kmatthews123/Controller/board_shematic/controller board V2/controller board v2/controller board v2.jpg

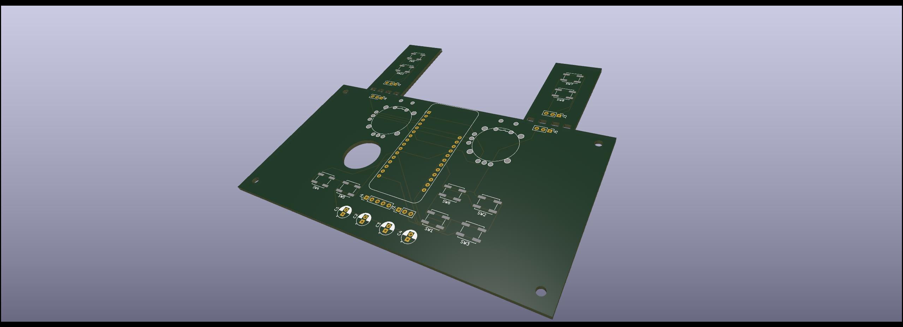
board_shematic/controller board V2/controller board v2/controller board v2.jpg
