kmatthews123/Controller/images/Controller/51d31018ed18142a5b782d5dddd84811.png

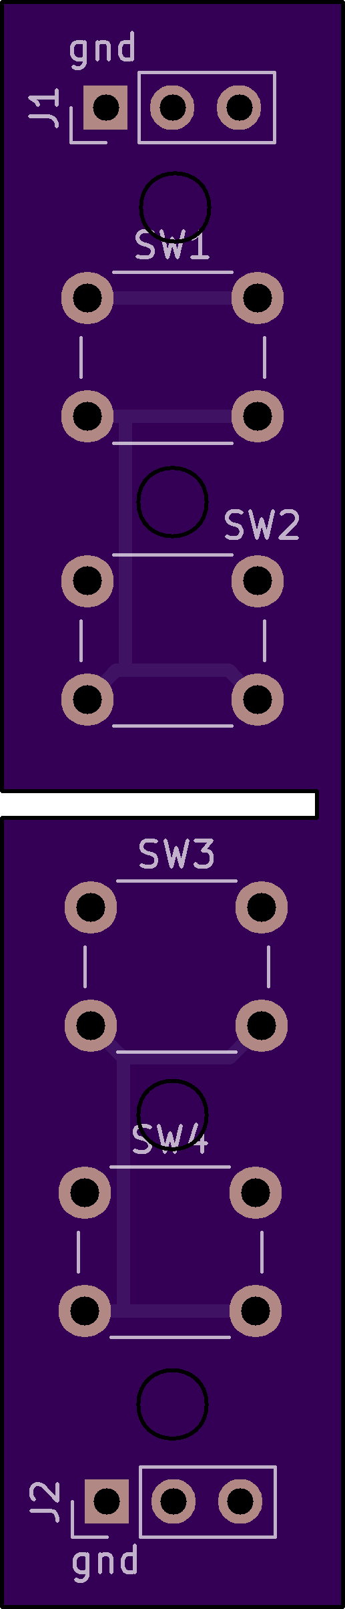
images/Controller/51d31018ed18142a5b782d5dddd84811.png
