kmatthews123/Controller/images/Controller/20240217_172748.jpg

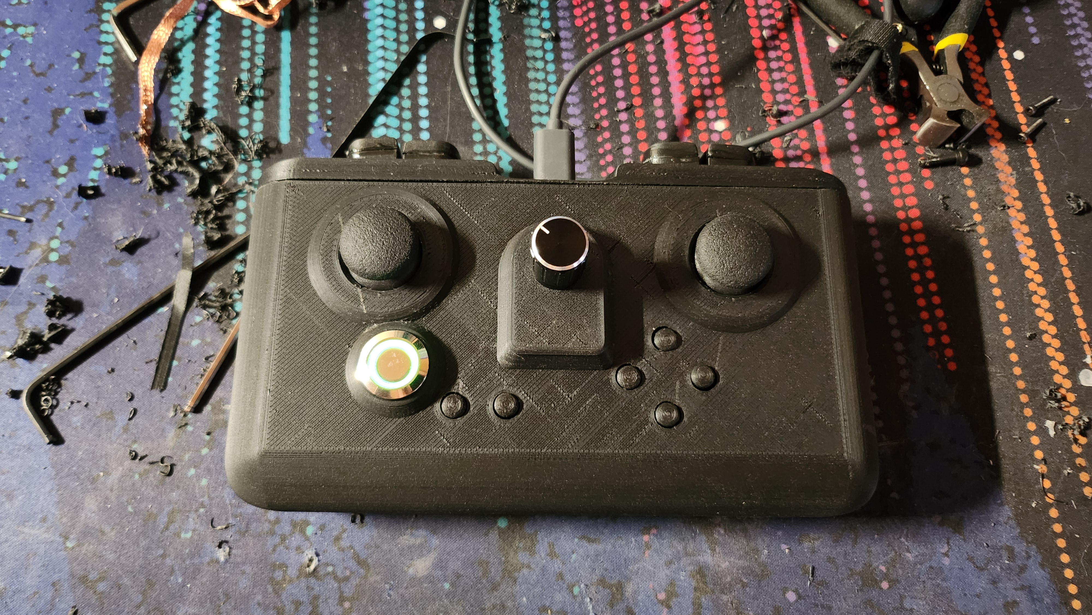
images/Controller/20240217_172748.jpg
