kmatthews123/Controller/images/Controller/20240217_172800.jpg

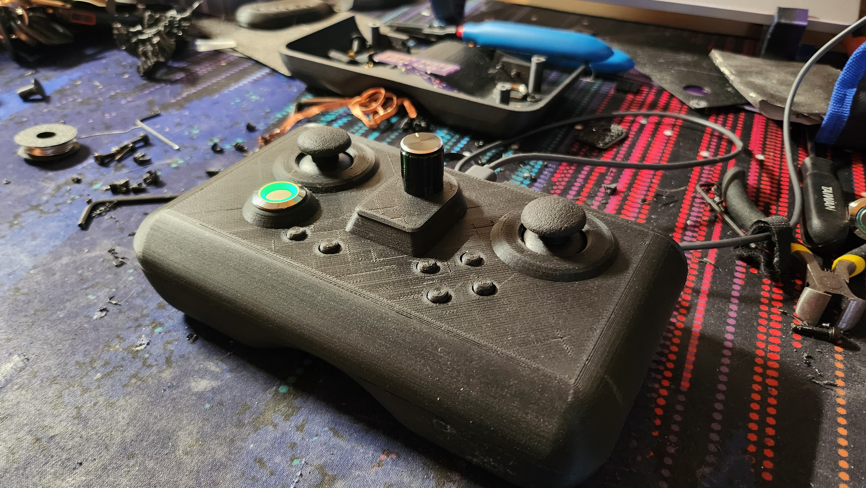
images/Controller/20240217_172800.jpg
