kmatthews123/Controller/images/Controller/20240217_172803.jpg

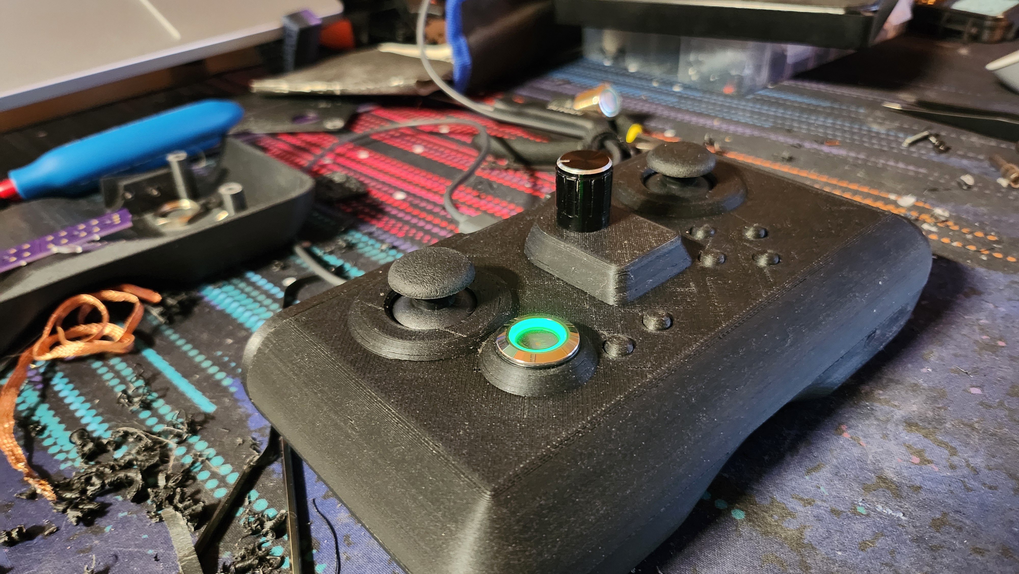
images/Controller/20240217_172803.jpg
