kmatthews123/Controller/images/Controller/20240221_180557.jpg

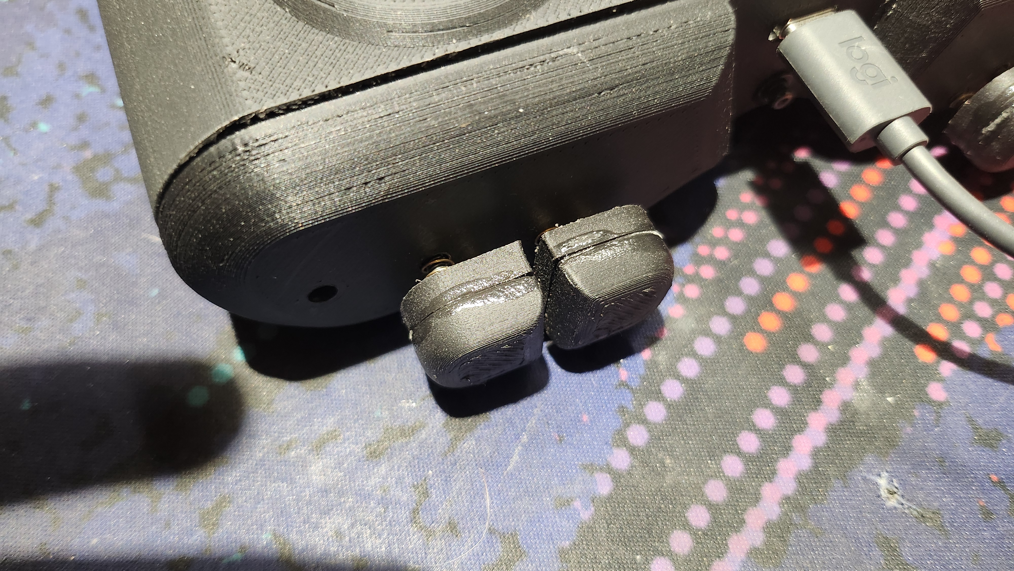
images/Controller/20240221_180557.jpg
