kmatthews123/Controller/images/Controller/20240221_180610.jpg

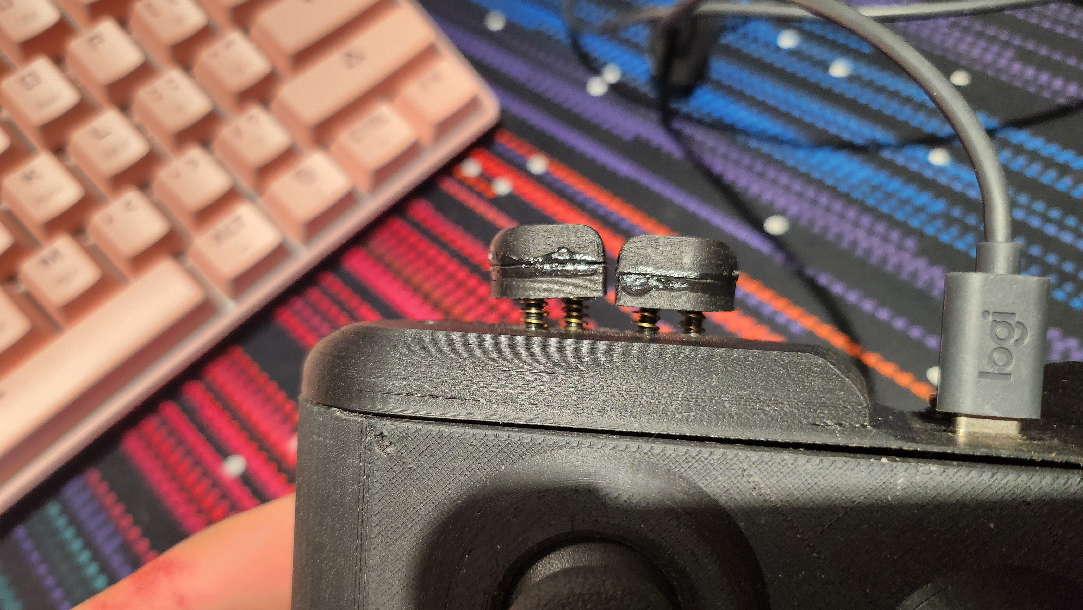
images/Controller/20240221_180610.jpg
