kmatthews123/Controller/images/Controller/20240221_180614.jpg

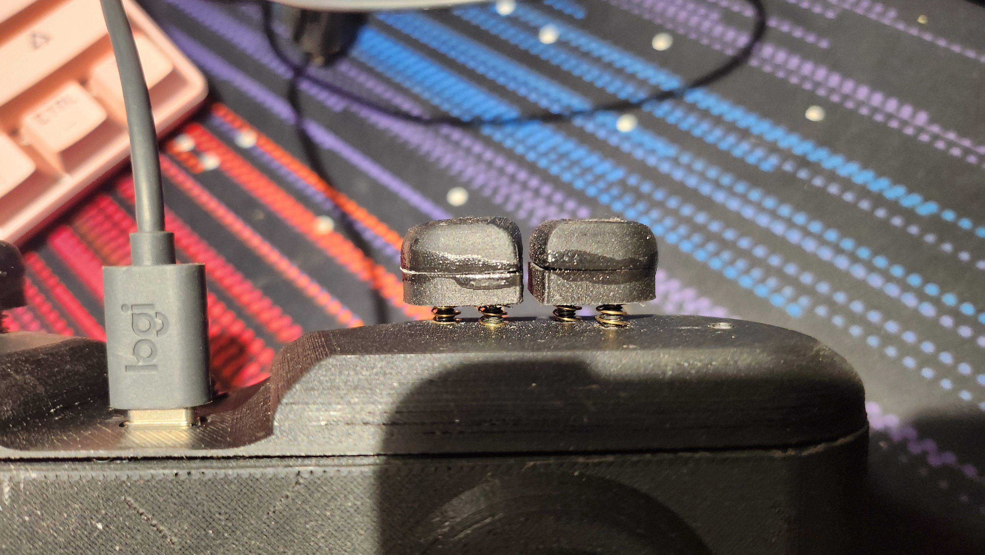
images/Controller/20240221_180614.jpg
