kmatthews123/Controller/images/Controller/controller board v2 back.png

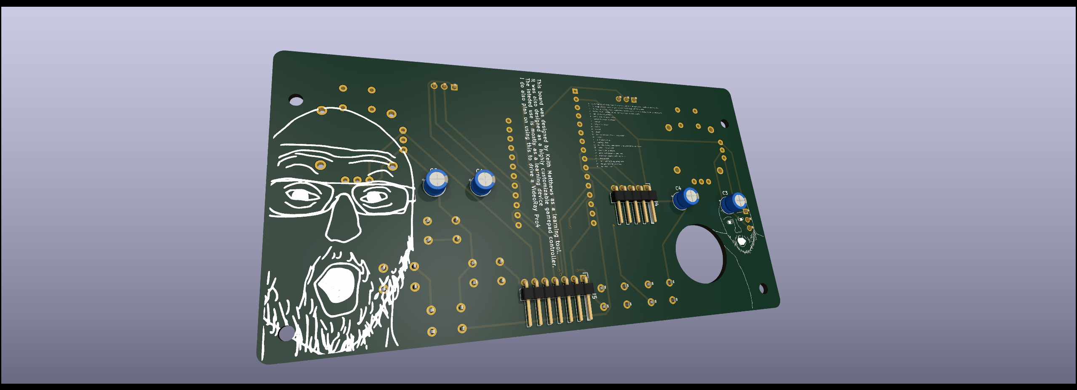
images/Controller/controller board v2 back.png
