kmatthews123/Controller/images/Controller/controller board v2.png

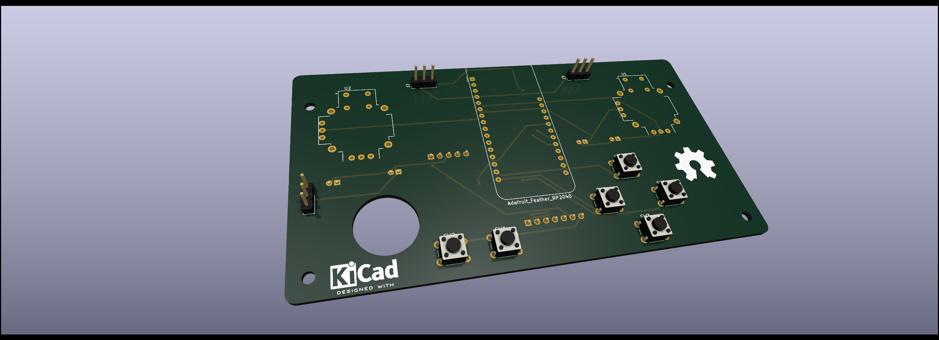
images/Controller/controller board v2.png
