kmatthews123/Controller/images/Controller/febf4503518cea3cbbaec0d58e9b9419.png

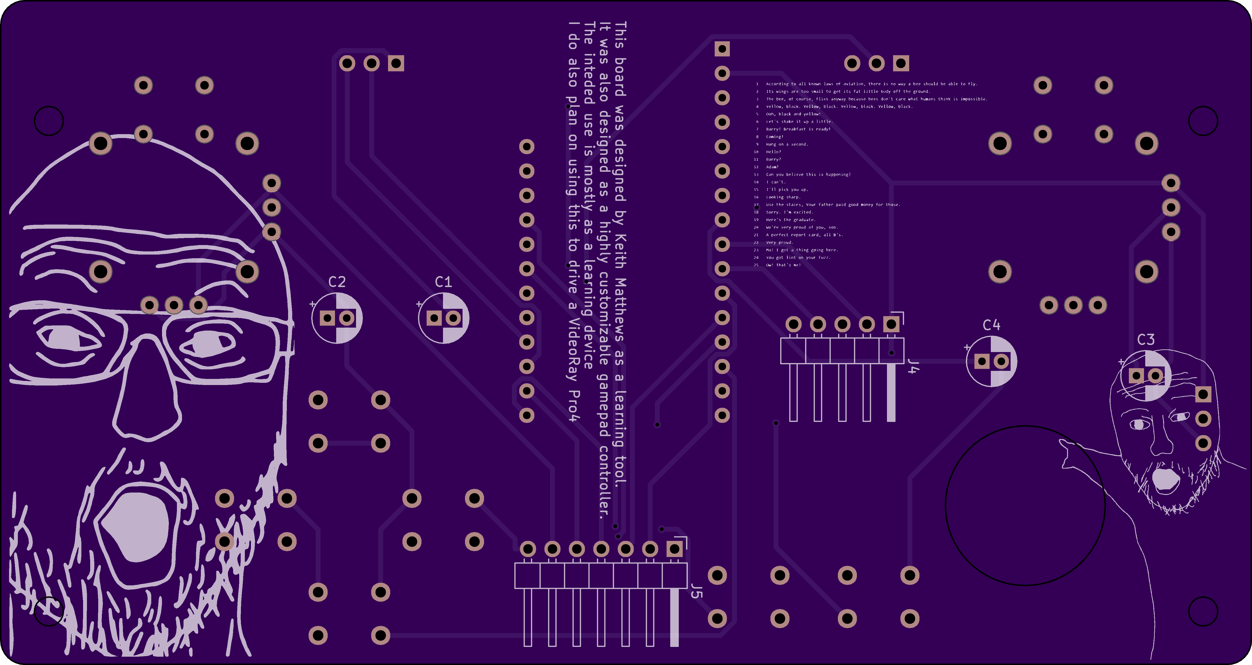
images/Controller/febf4503518cea3cbbaec0d58e9b9419.png
