kmatthews123/Controller/images/Guitar/20231124_203415.jpg

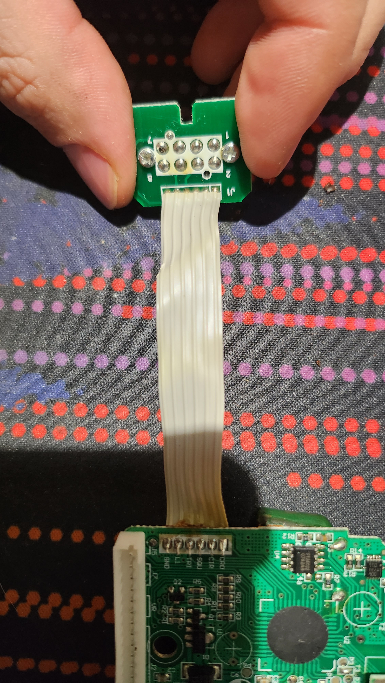
images/Guitar/20231124_203415.jpg
