kmatthews123/Controller/images/Guitar/20231124_203419.jpg

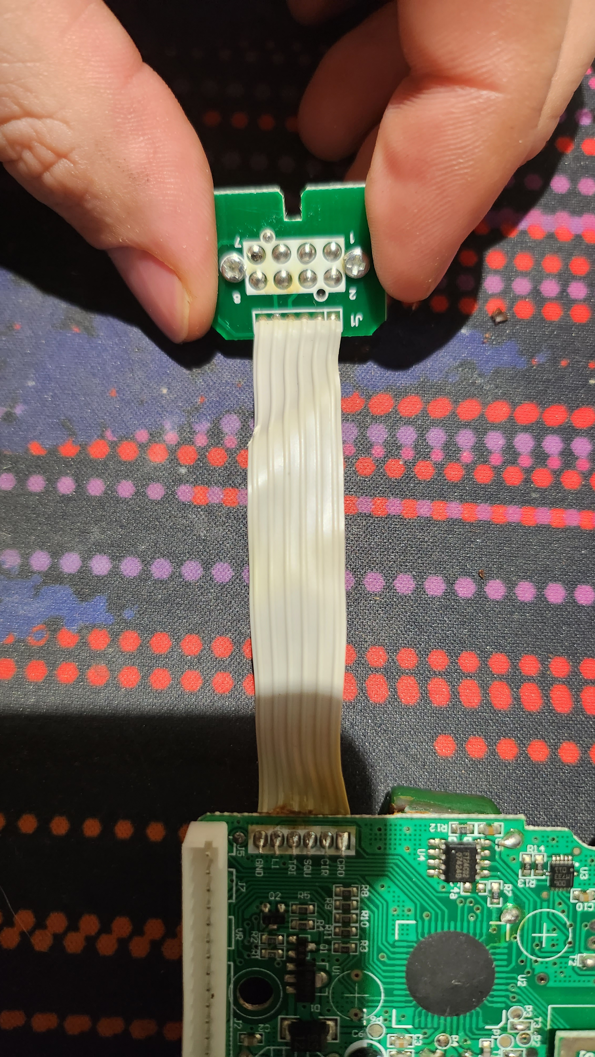
images/Guitar/20231124_203419.jpg
