kmatthews123/Controller/images/Refrence images/adafruit_products_feather-rp2040-pins.png

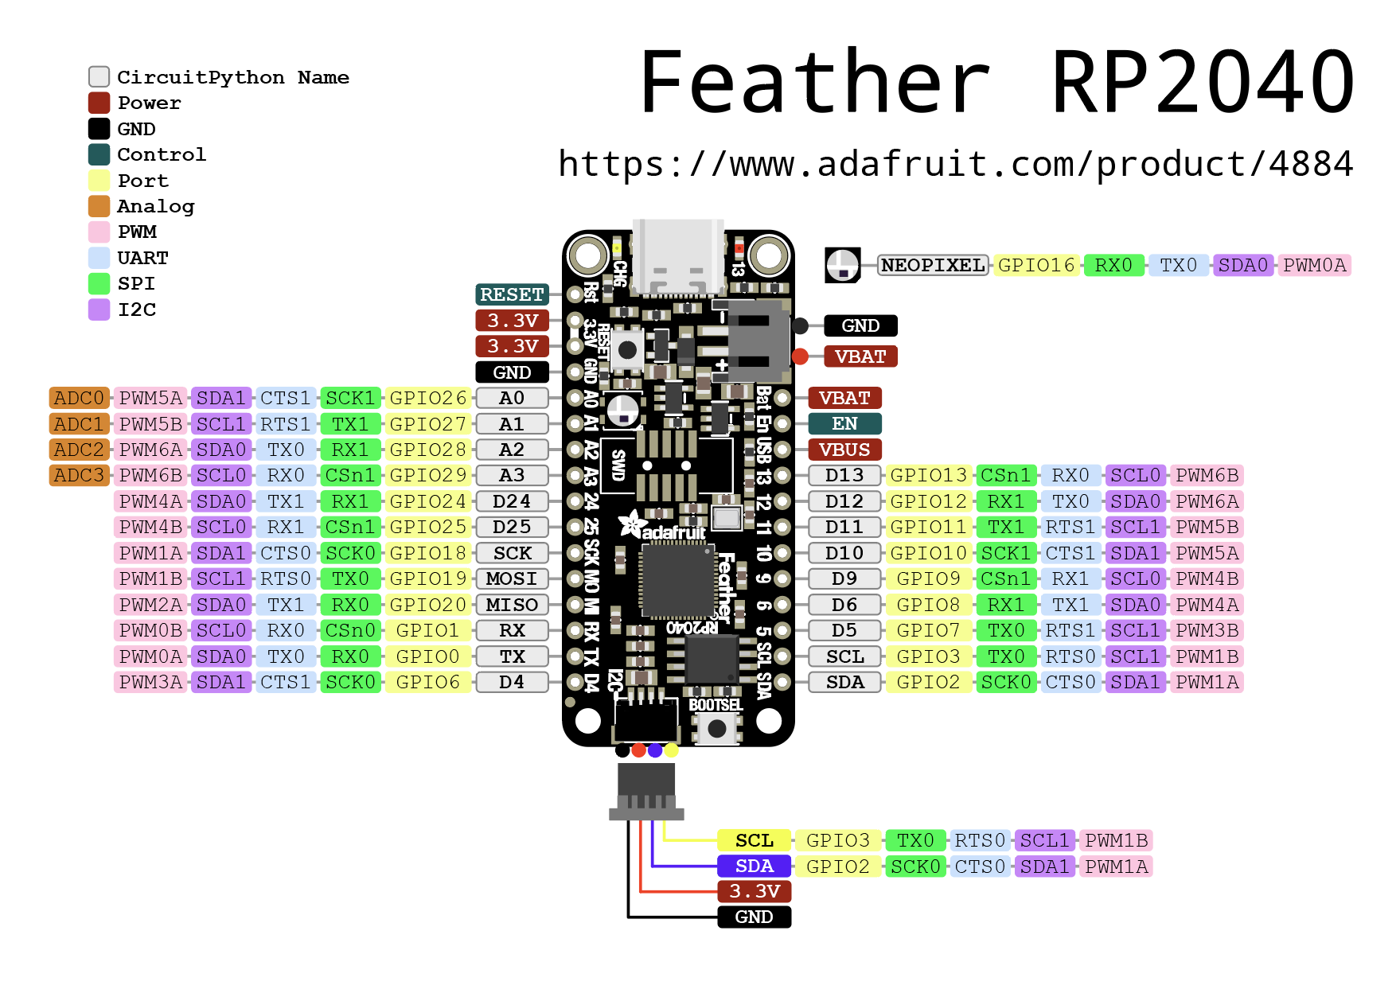
images/Refrence images/adafruit_products_feather-rp2040-pins.png
