kmatthews123/Controller/images/Refrence images/cover2.jpg

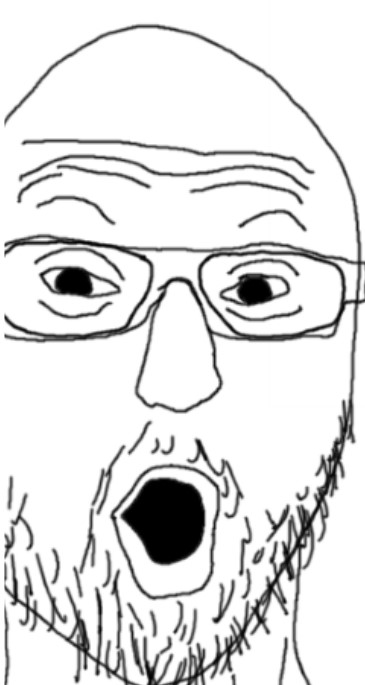
images/Refrence images/cover2.jpg
