kmatthews123/Controller/images/Refrence images/Drawing 2024-01-11 20.26.41.excalidraw 1.png

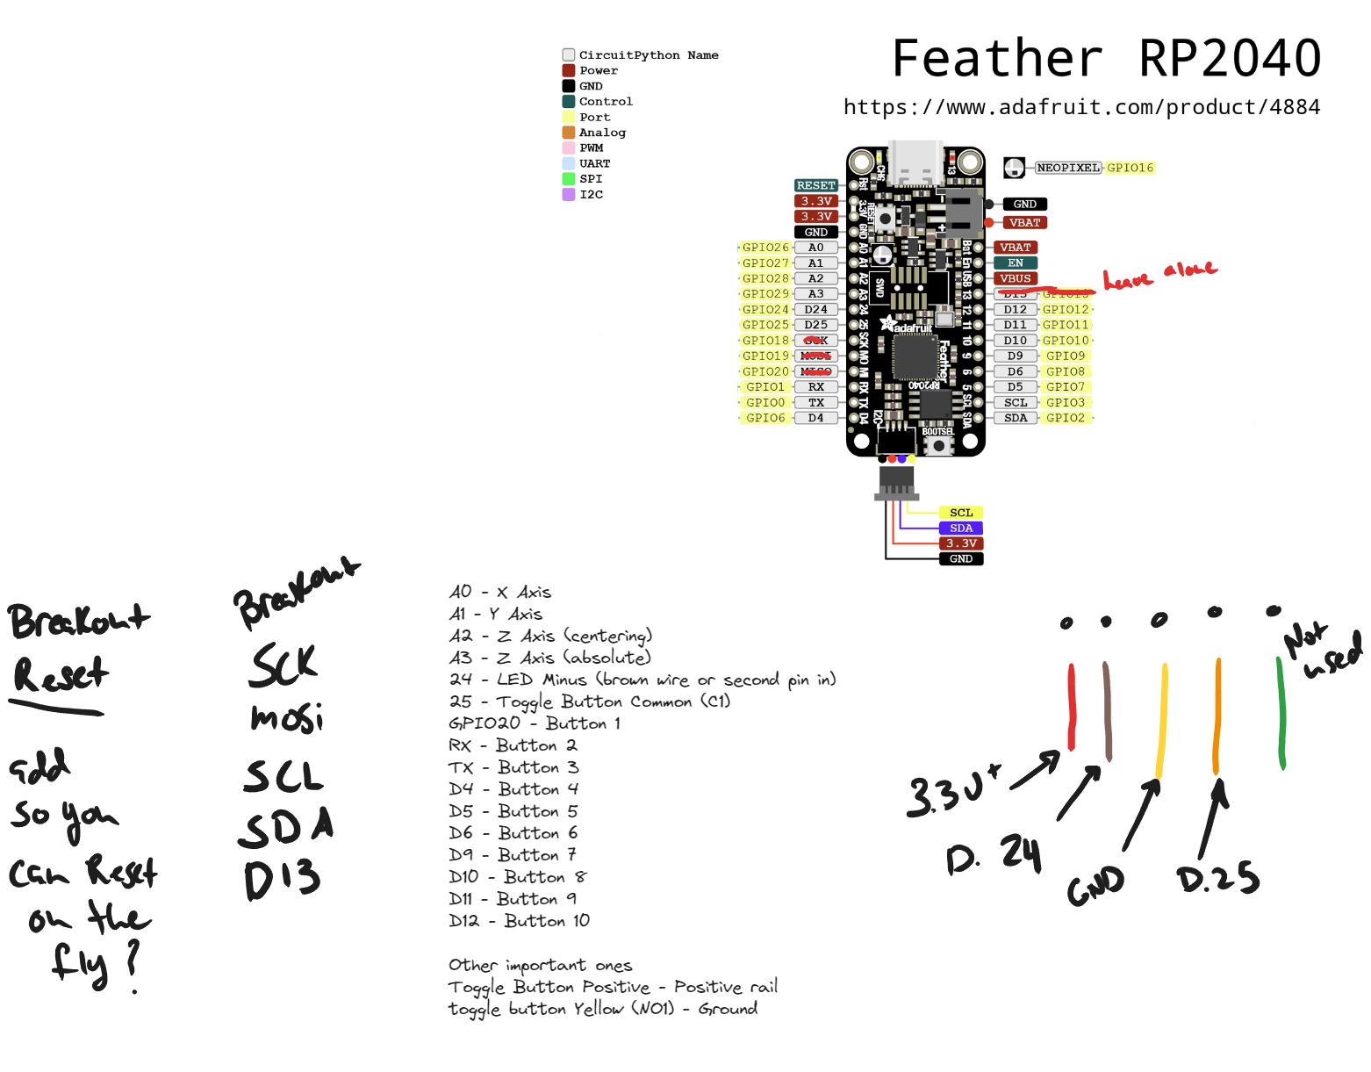
images/Refrence images/Drawing 2024-01-11 20.26.41.excalidraw 1.png
