kmatthews123/Controller/images/Refrence images/image67.png

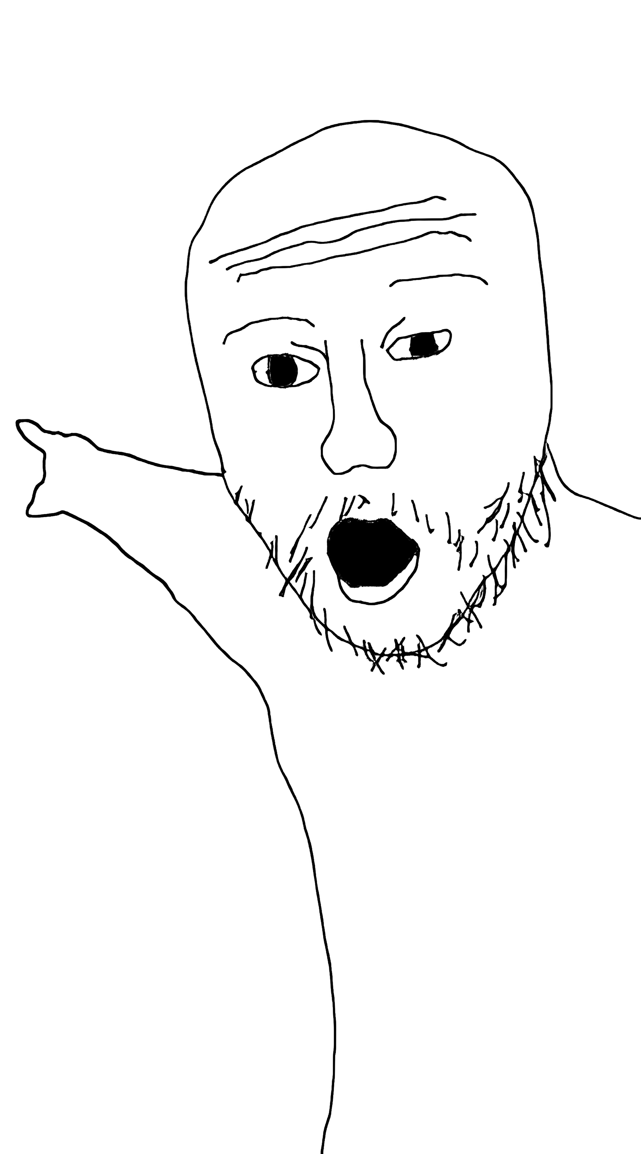
images/Refrence images/image67.png
