kmatthews123/Controller/images/Refrence images/kb2040 pinnout.png

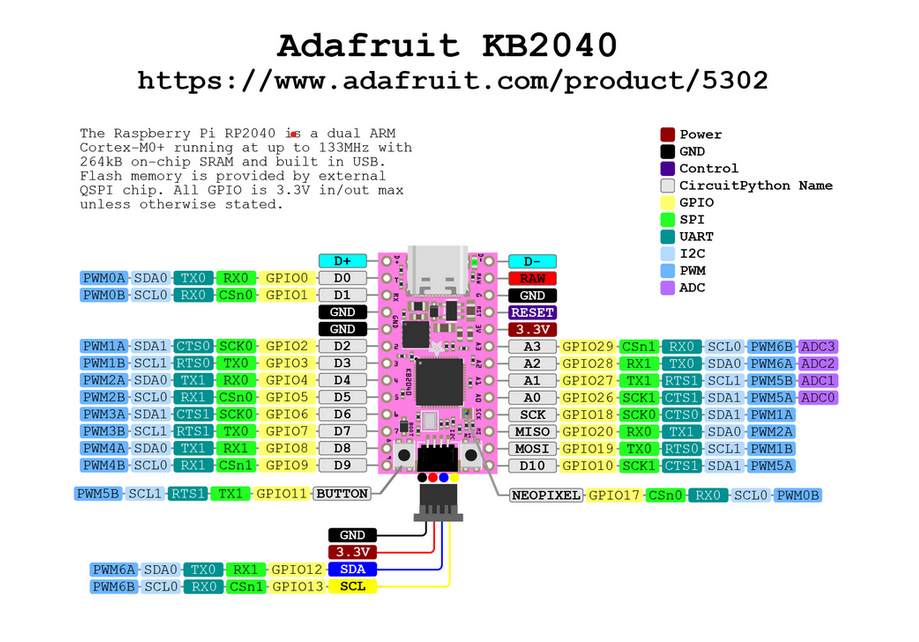
images/Refrence images/kb2040 pinnout.png
