kmatthews123/Controller/3d models/controller body 3d print files/Controller body - faceplate.3mf

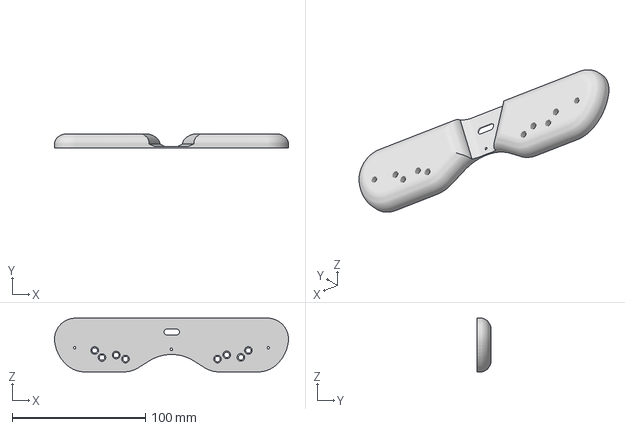
[picture p41: CAD file, 2024-02-18]
3d models/controller body 3d print files/Controller body - faceplate.3mf
175.4 x 10.6 x 40.3 mm
