kmatthews123/Controller/3d models/controller body 3d print files/Controller body - top shell.3mf

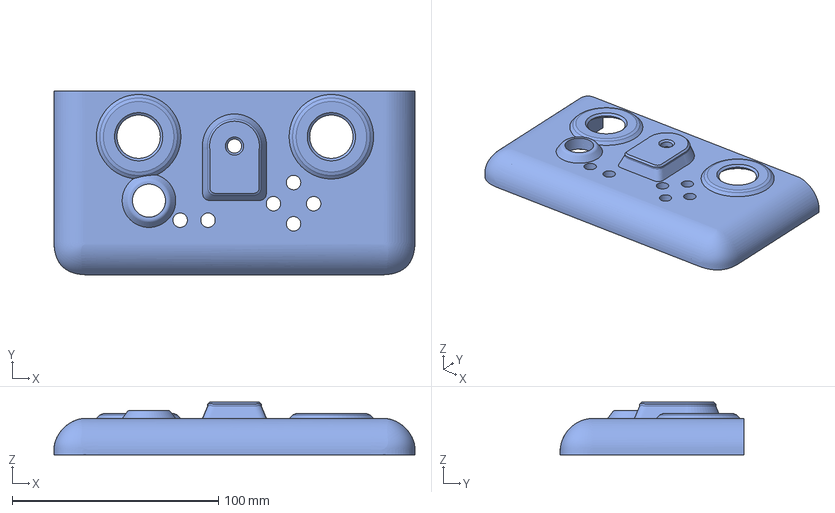
[picture p42: CAD file, 2024-02-18]
3d models/controller body 3d print files/Controller body - top shell.3mf
175.1 x 89.2 x 25.6 mm
