kmatthews123/Controller/code/Code for Feather Pico/boot.py

"""JoystickXL minimal boot.py."""

import usb_hid  # type: ignore (this is a CircuitPython built-in)
from joystick_xl.hid import create_joystick

# This will enable a joystick USB HID device.  All other standard CircuitPython USB HID
# devices (keyboard, mouse, consumer control) will be disabled.
usb_hid.enable((create_joystick(axes=6, buttons=12, hats=0),))
